LaskaKit/ESPink-Shelf/SW/Date_BusConnection_WeatherForecast/Bus.h

    // departures in working days
    // {Hour, FirstDepartureInMinutes, SecondDepartureInMinutes, ...}
    static int busDepartureWD[][18] = {
                  {4, 46, -1, -1, -1, -1, -1, -1, -1, -1}, //first hour of departure
                  {5, 6, 23, 38, 50, -1, -1, -1, -1, -1}, 
                  {6, 1, 9, 17, 25, 33, 41, 49, 56, -1}, 
                  {7, 4, 11, 19, 26, 34, 41, 49, 56, -1},
                  {8, 4, 11, 19, 29, 39, 51, -1, -1, -1},
                  {9, 6, 21, 36, 51, -1, -1, -1, -1, -1},
                  {10, 6, 21, 36, 51, -1, -1, -1, -1, -1},
                  {11, 6, 21, 36, 51, -1, -1, -1, -1, -1},
                  {12, 6, 21, 36, 51, -1, -1, -1, -1, -1},
                  {13, 6, 19, 31, 43, 55, -1, -1, -1, -1},
                  {14, 7, 17, 27, 37, 47, 57, -1, -1, -1},
                  {15, 7, 16, 24, 31, 39, 46, 54, -1, -1},
                  {16, 1, 9, 16, 24, 31, 39, 46, 54, -1},
                  {17, 1, 9, 16, 24, 31, 39, 46, 54, -1},
                  {18, 1, 9, 16, 24, 31, 39, 47, 57, -1},
                  {19, 7, 18, 29, 42, 57, -1, -1, -1, -1},
                  {20, 12, 27, 47, -1, -1, -1, -1, -1, -1},
                  {21, 7, 27, 47, -1, -1, -1, -1, -1, -1},
                  {22, 7, 27, 47, -1, -1, -1, -1, -1, -1} // last hour of departure
                  };

  // Saturday departures
  static int busDepartureSat[][18] = {
                  {4, 57, -1, -1, -1, -1, -1, -1, -1, -1}, 
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
                  {19, 12, 27, 42, 57, -1, -1, -1, -1, -1},
                  {20, 12, 27, 47, -1, -1, -1, -1, -1, -1},
                  {21, 7, 27, 47, -1, -1, -1, -1, -1, -1},
                  {22, 7, 27, 47, -1, -1, -1, -1, -1, -1}
                  };
